micromouseonline/micromouse-timer/hardware/seven-segment-display/single-digit-mask-gray.png

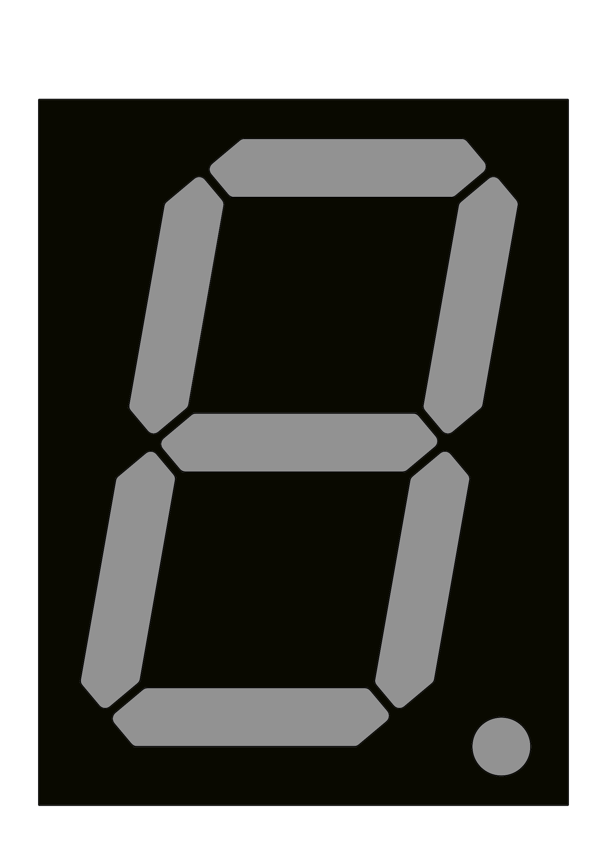
hardware/seven-segment-display/single-digit-mask-gray.png
