micromouseonline/micromouse-timer/images/controller-breadboard-prototype.jpg

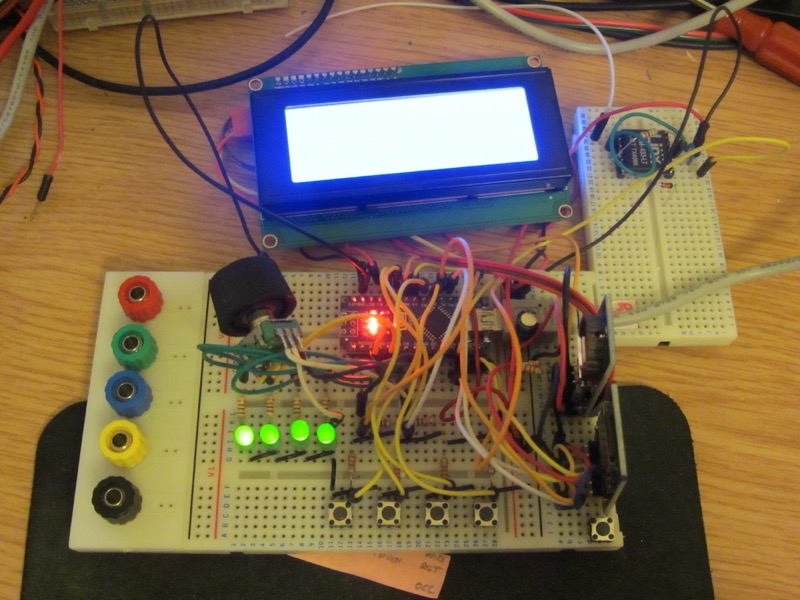
images/controller-breadboard-prototype.jpg
