micromouseonline/micromouse-timer/images/controller-panel-template.jpg

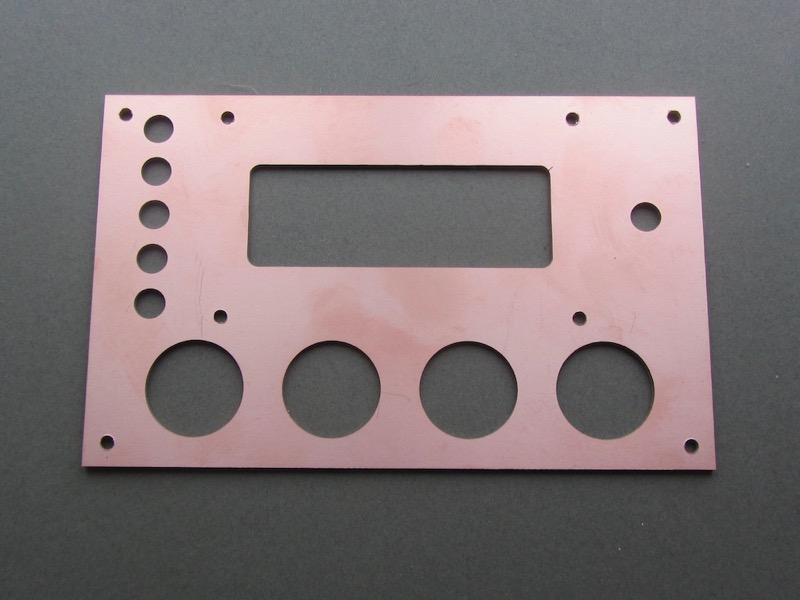
images/controller-panel-template.jpg
