micromouseonline/micromouse-timer/images/controller-render-V2.png

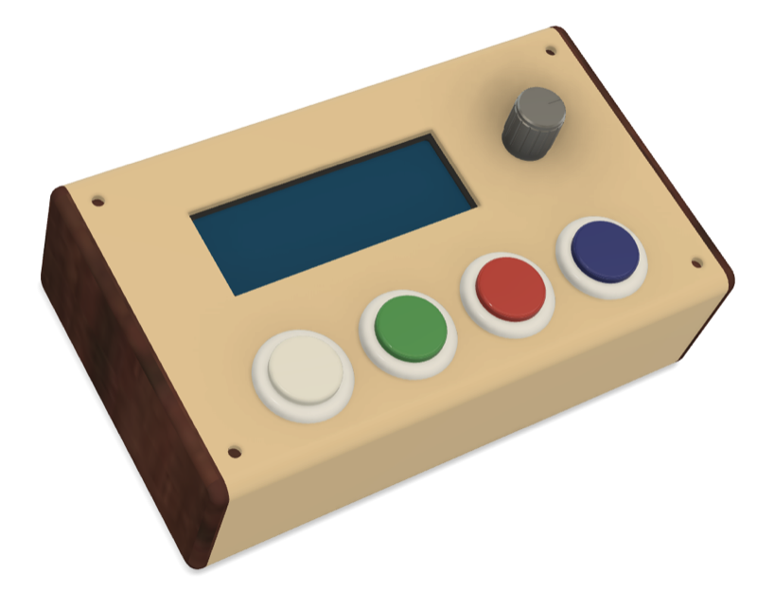
images/controller-render-V2.png
