micromouseonline/micromouse-timer/images/wall-pcb-with-led-holder.png

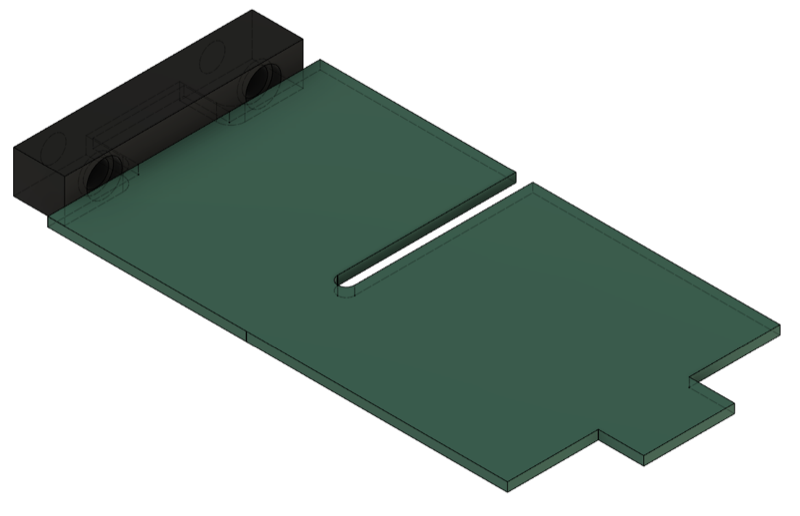
images/wall-pcb-with-led-holder.png
