micromouseonline/micromouse-timer/images/controller-assembly-prototype-parts.jpg

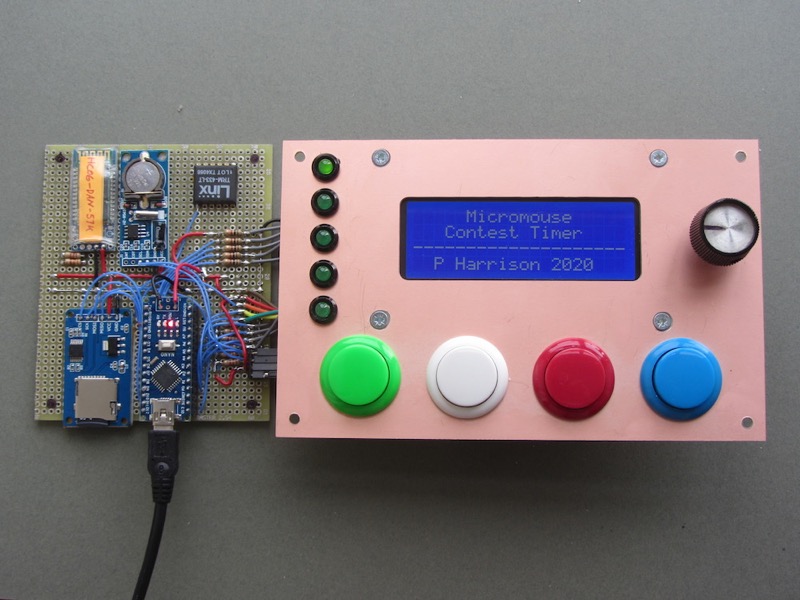
images/controller-assembly-prototype-parts.jpg
