micromouseonline/micromouse-timer/images/timing-gate-parts.jpg

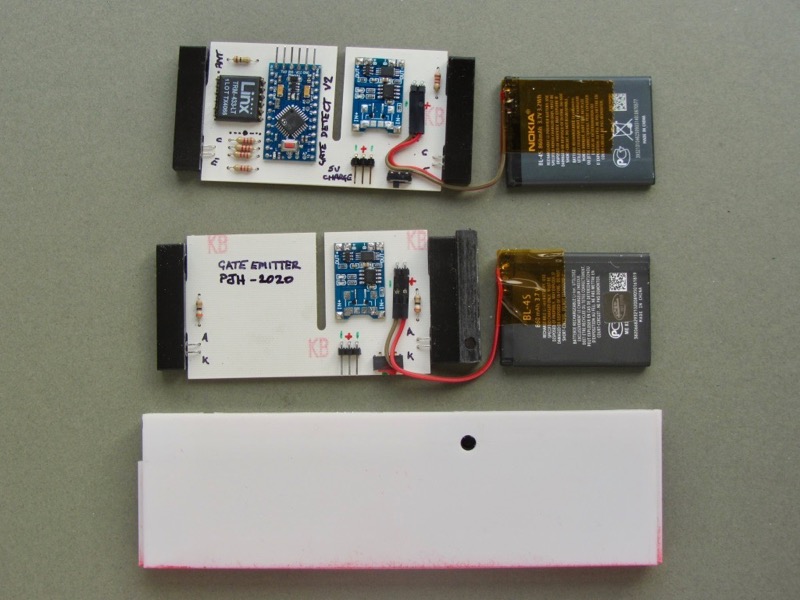
images/timing-gate-parts.jpg
