micromouseonline/micromouse-timer/hardware/gate-detector/gate-detector-mirrored (copy).dxf

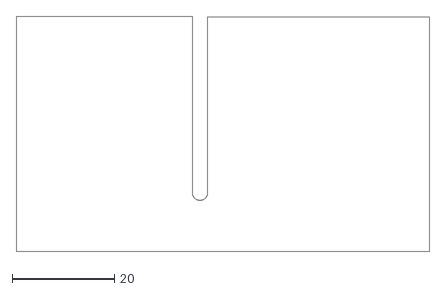
[picture p28: CAD file, 2023-07-05]
hardware/gate-detector/gate-detector-mirrored (copy).dxf
81.1 x 46.1
