micromouseonline/micromouse-timer/hardware/seven-segment-display/seven-segment-body-upright-milled.dxf

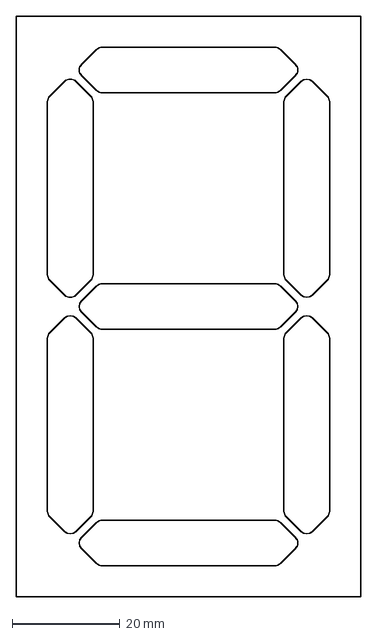
[picture p29: CAD file, 2023-07-05]
hardware/seven-segment-display/seven-segment-body-upright-milled.dxf
64.0 x 108.0 mm
