micromouseonline/micromouse-timer/hardware/controller-enclosure/controller-panel.stl

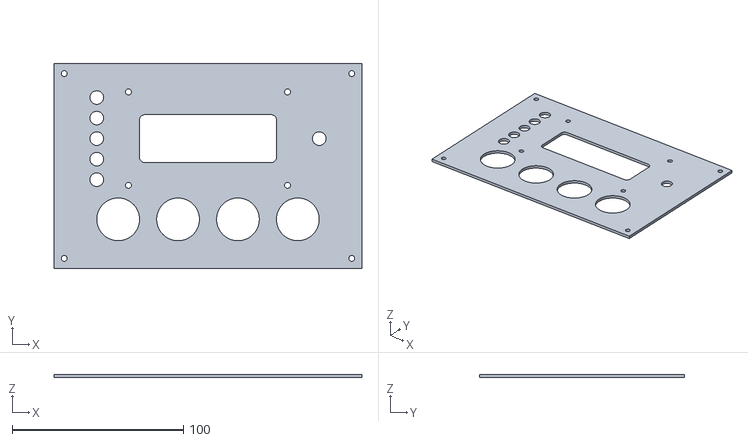
[picture p30: CAD file, 2023-07-05]
hardware/controller-enclosure/controller-panel.stl
180.0 x 120.0 x 2.00
