micromouseonline/micromouse-timer/hardware/controller-pcb/gate-controller-case-body.stl

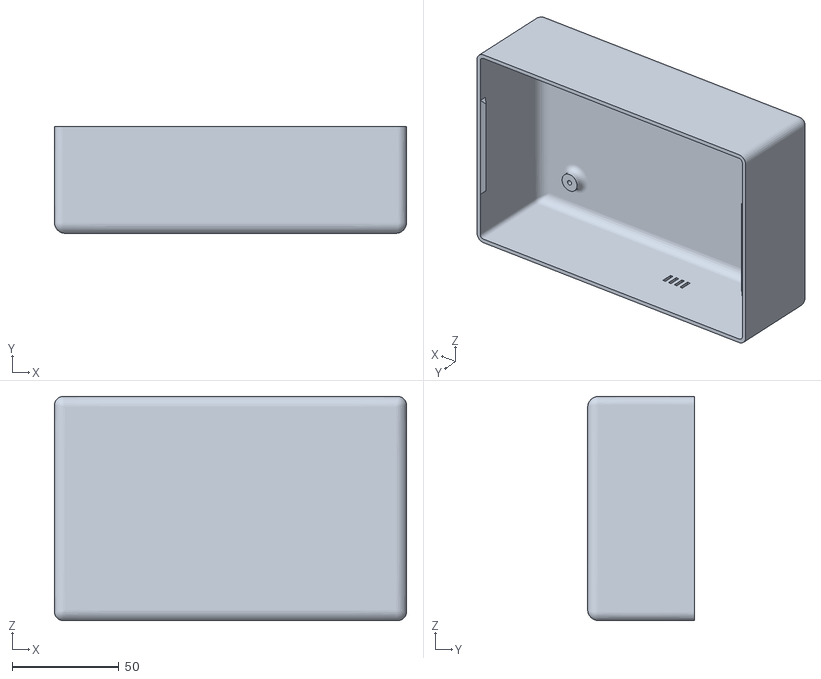
[picture p31: CAD file, 2023-07-05]
hardware/controller-pcb/gate-controller-case-body.stl
165.0 x 50.0 x 105.0
