micromouseonline/micromouse-timer/hardware/gate-charger/4-way-charger-brd-nofill.dxf

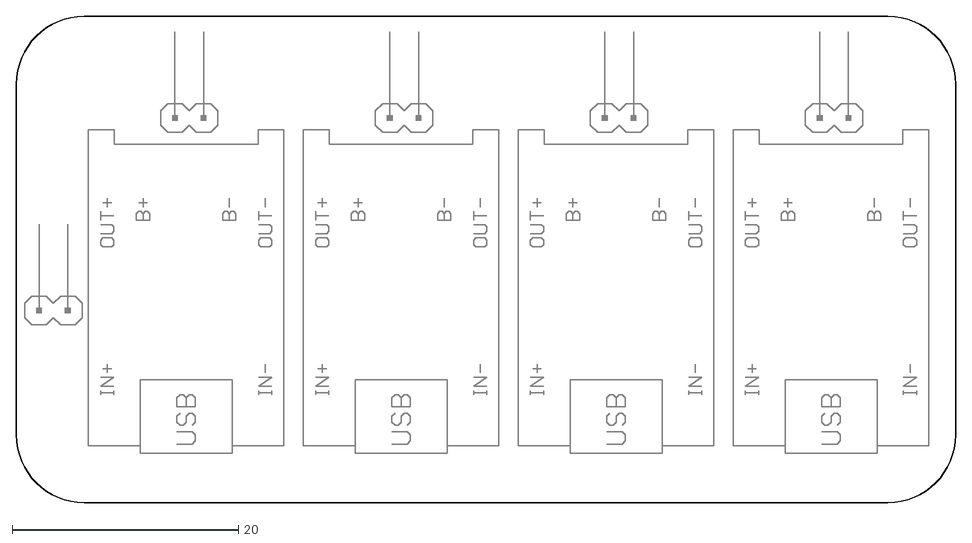
[picture p32: CAD file, 2023-07-05]
hardware/gate-charger/4-way-charger-brd-nofill.dxf
83.0 x 43.0
