micromouseonline/micromouse-timer/hardware/gate-detector/gate-detector-mirrored.dxf

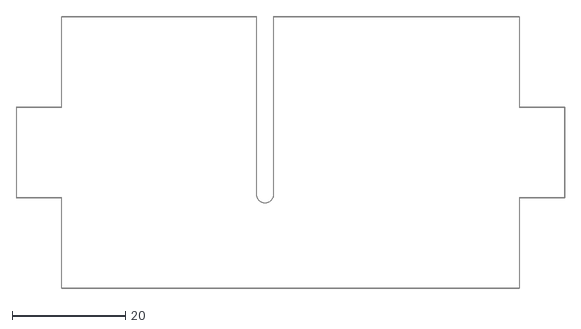
[picture p33: CAD file, 2023-07-05]
hardware/gate-detector/gate-detector-mirrored.dxf
97.1 x 48.1
