micromouseonline/micromouse-timer/hardware/gate-post-and-wall-parts/detector-holder.stl

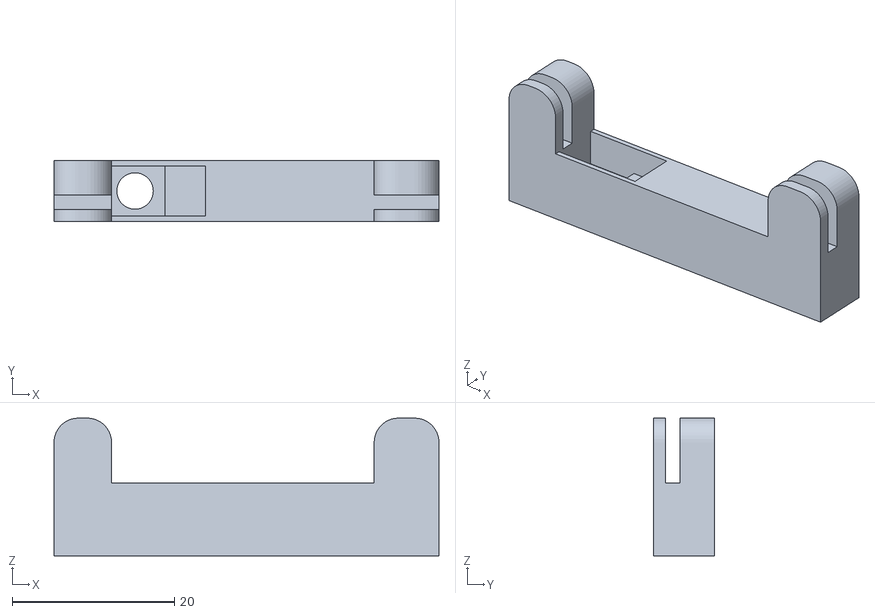
[picture p34: CAD file, 2023-07-05]
hardware/gate-post-and-wall-parts/detector-holder.stl
47.5 x 7.50 x 17.0
