micromouseonline/micromouse-timer/hardware/seven-segment-display/seven-segment-body-upright-segment.stl

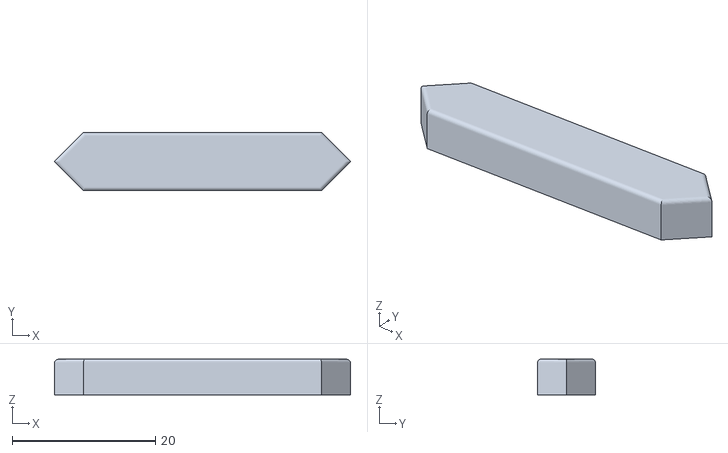
[picture p35: CAD file, 2023-07-05]
hardware/seven-segment-display/seven-segment-body-upright-segment.stl
41.3 x 8.10 x 5.00
