micromouseonline/micromouse-timer/hardware/controller-pcb/gate-controller-mirrored-V2.dxf

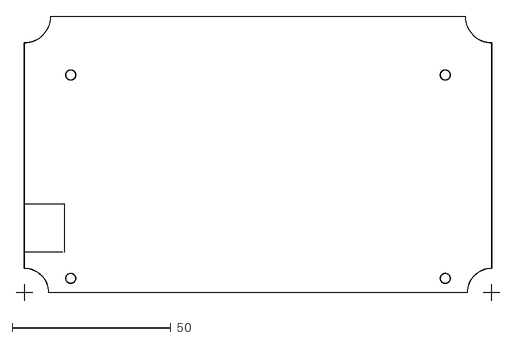
[picture p36: CAD file, 2023-07-05]
hardware/controller-pcb/gate-controller-mirrored-V2.dxf
152.6 x 89.8
