micromouseonline/micromouse-timer/hardware/gate-post-and-wall-parts/maze-gate-emitter-detector-holder-v2.stl

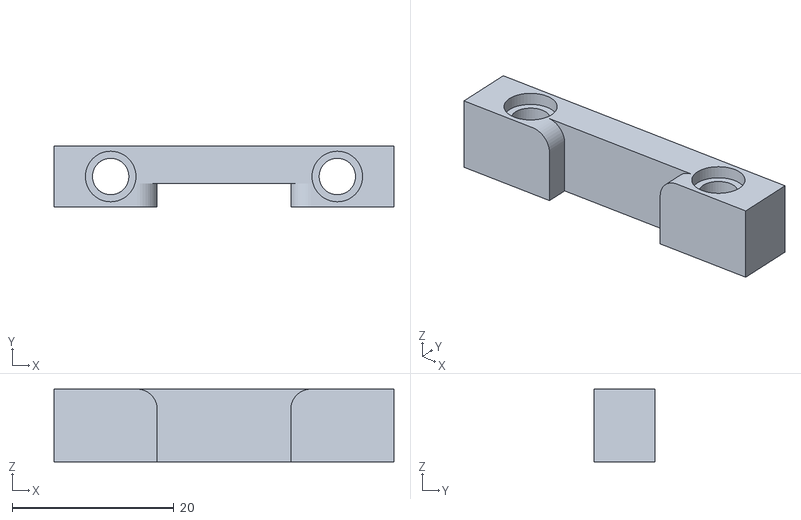
[picture p37: CAD file, 2023-07-05]
hardware/gate-post-and-wall-parts/maze-gate-emitter-detector-holder-v2.stl
42.0 x 7.50 x 9.00
