micromouseonline/micromouse-timer/hardware/seven-segment-display/vertical-segment.stl

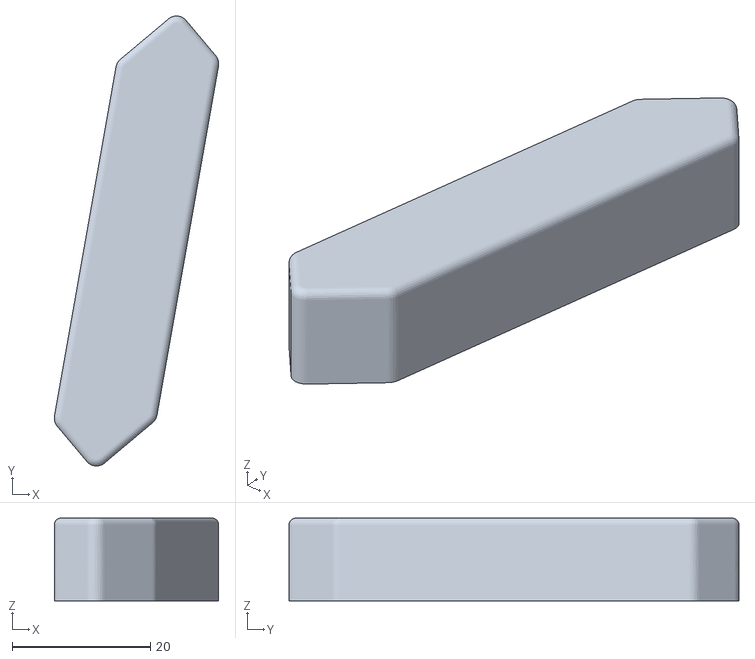
[picture p38: CAD file, 2023-07-05]
hardware/seven-segment-display/vertical-segment.stl
23.8 x 65.1 x 12.0
