micromouseonline/micromouse-timer/hardware/gate-post-and-wall-parts/post-half-double-sensor.stl

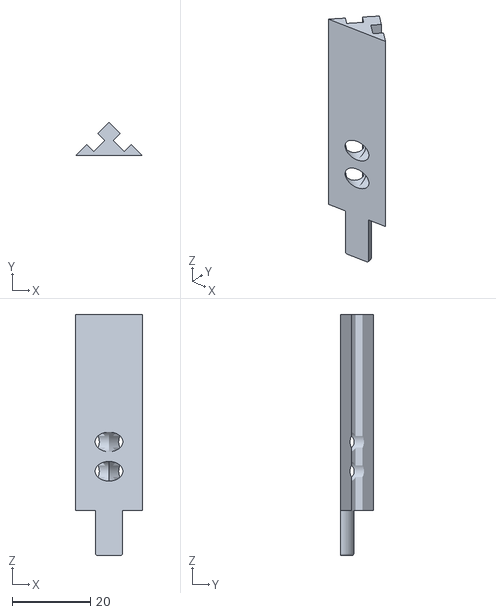
[picture p39: CAD file, 2023-07-05]
hardware/gate-post-and-wall-parts/post-half-double-sensor.stl
17.0 x 8.49 x 61.5
