micromouseonline/micromouse-timer/hardware/seven-segment-display/vertical-segment-small.stl

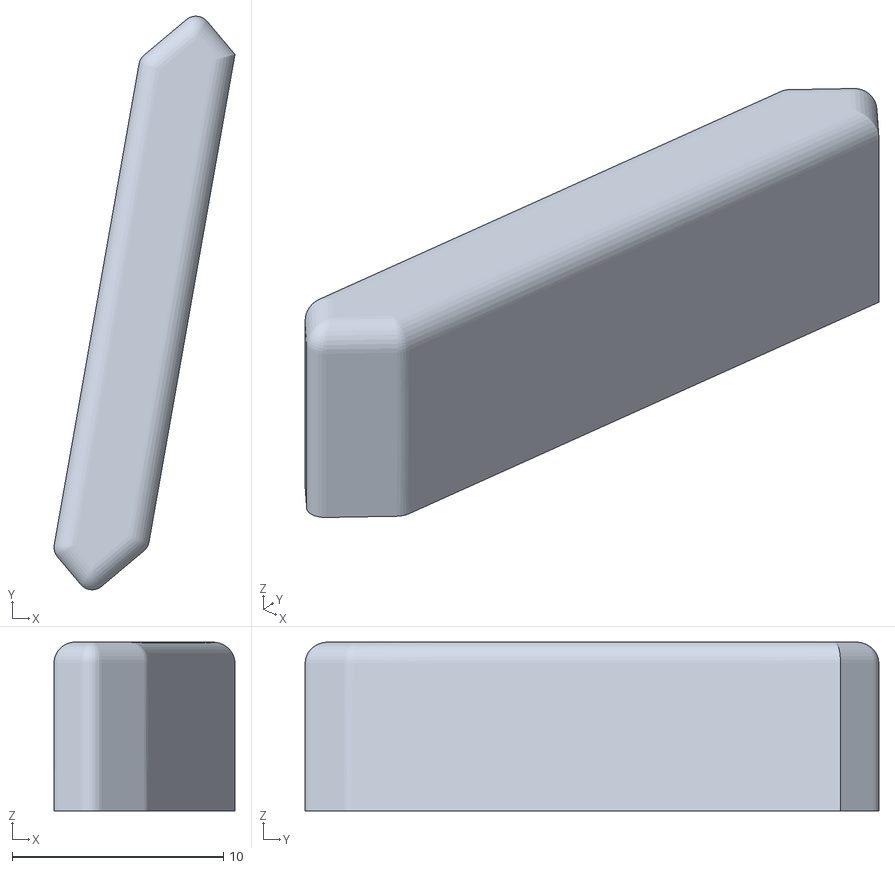
[picture p40: CAD file, 2023-07-05]
hardware/seven-segment-display/vertical-segment-small.stl
8.57 x 27.2 x 8.00
