micromouseonline/micromouse-timer/hardware/controller-enclosure/spacer-9.6mm.stl

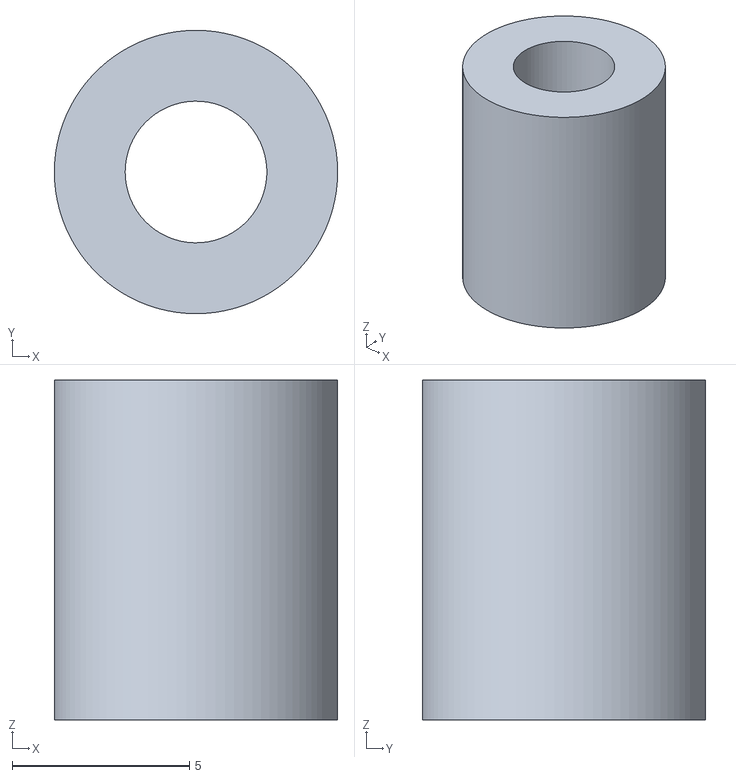
[picture p41: CAD file, 2023-07-05]
hardware/controller-enclosure/spacer-9.6mm.stl
8.00 x 8.00 x 9.60
