micromouseonline/micromouse-timer/hardware/gate-post-and-wall-parts/emitter-detector-twin-holder.stl

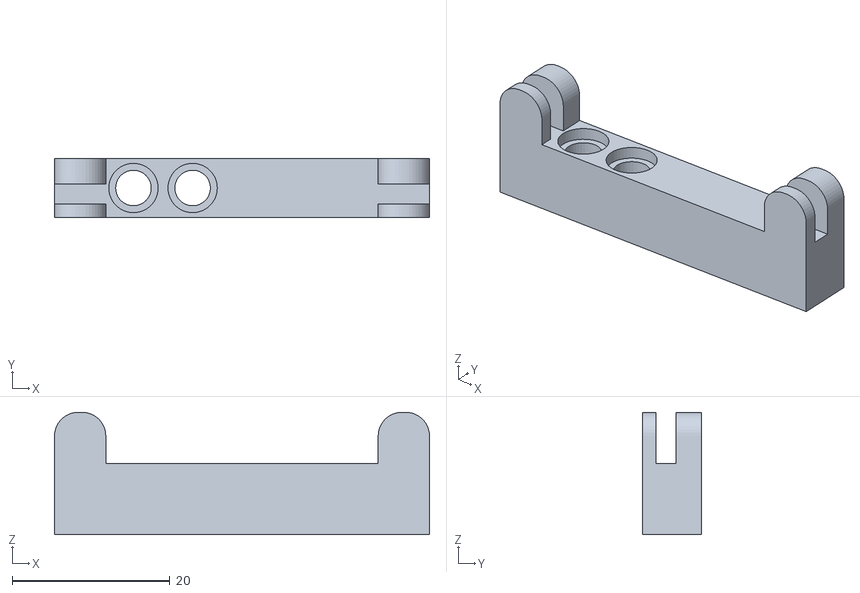
[picture p42: CAD file, 2023-07-05]
hardware/gate-post-and-wall-parts/emitter-detector-twin-holder.stl
47.5 x 7.50 x 15.5
