micromouseonline/micromouse-timer/hardware/seven-segment-display/seven-segment-body-small.stl

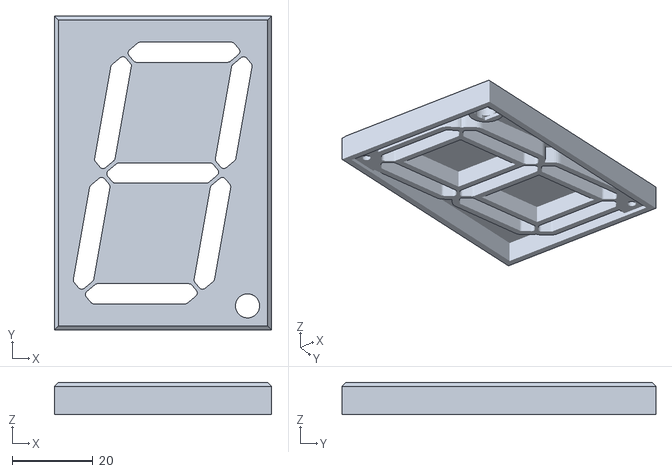
[picture p43: CAD file, 2023-07-05]
hardware/seven-segment-display/seven-segment-body-small.stl
54.0 x 78.0 x 8.00
