micromouseonline/micromouse-timer/hardware/gate-post-and-wall-parts/presence-reflector.stl

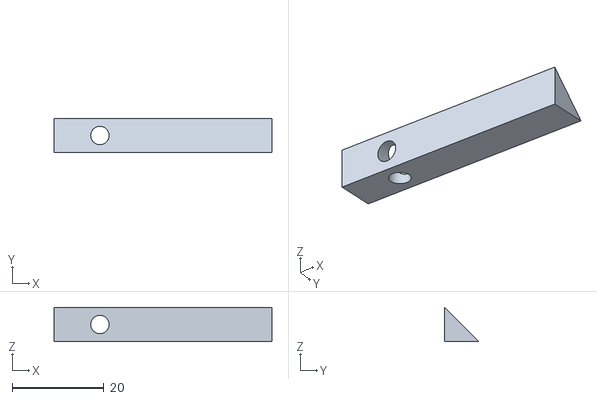
[picture p44: CAD file, 2023-07-05]
hardware/gate-post-and-wall-parts/presence-reflector.stl
47.5 x 7.50 x 7.50
