micromouseonline/micromouse-timer/hardware/seven-segment-display/single digit.dxf

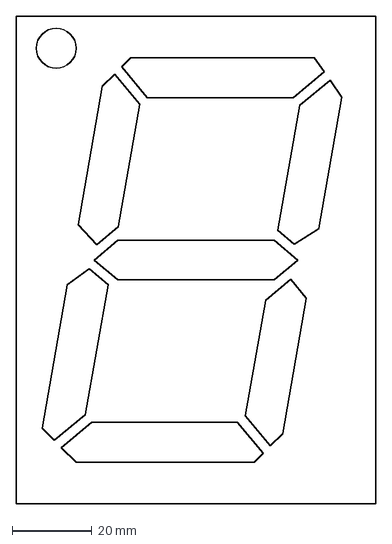
[picture p45: CAD file, 2023-07-05]
hardware/seven-segment-display/single digit.dxf
90.0 x 122.0 mm
