micromouseonline/micromouse-timer/hardware/controller-enclosure/gate-controller-V2.dxf

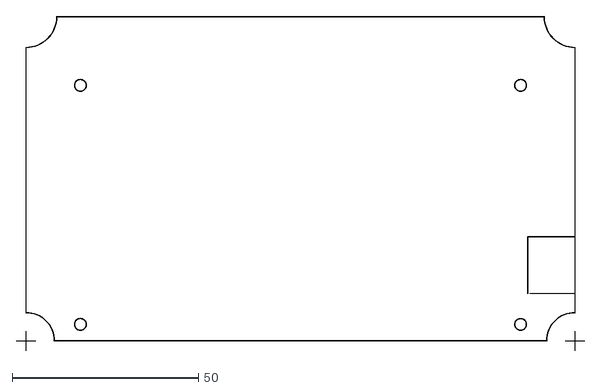
[picture p46: CAD file, 2023-07-05]
hardware/controller-enclosure/gate-controller-V2.dxf
152.6 x 89.8
