micromouseonline/micromouse-timer/hardware/gate-post-and-wall-parts/detector-holder-v2.stl

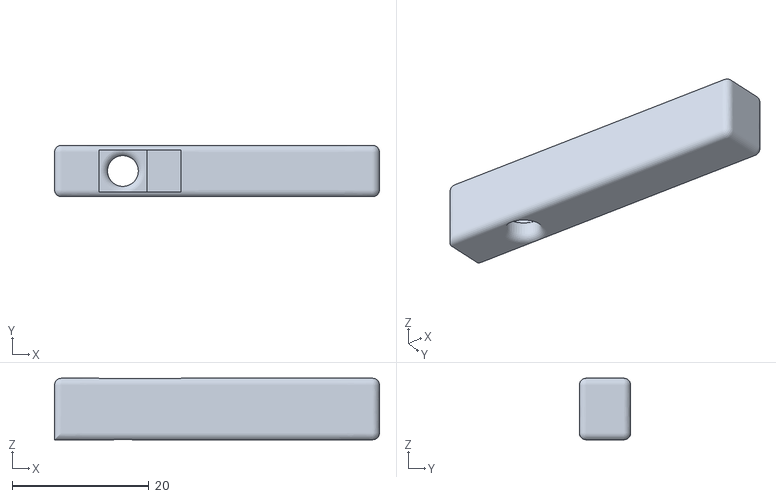
[picture p47: CAD file, 2023-07-05]
hardware/gate-post-and-wall-parts/detector-holder-v2.stl
47.5 x 7.50 x 9.00
