micromouseonline/micromouse-timer/hardware/seven-segment-display/display-connectors.dxf

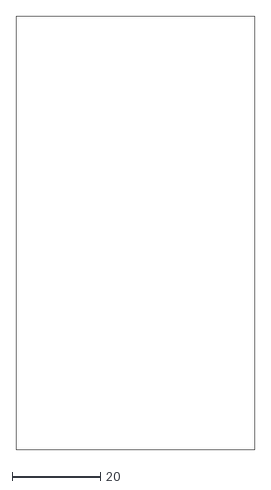
[picture p48: CAD file, 2023-07-05]
hardware/seven-segment-display/display-connectors.dxf
54.0 x 98.0
