micromouseonline/micromouse-timer/hardware/seven-segment-display/seven-segment-body-upright.stl

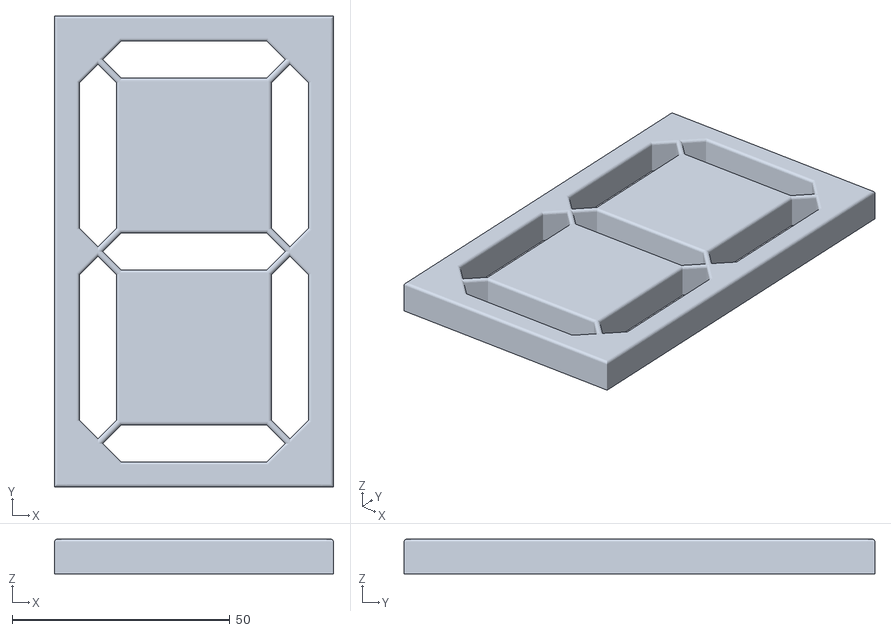
[picture p49: CAD file, 2023-07-05]
hardware/seven-segment-display/seven-segment-body-upright.stl
64.0 x 108.0 x 8.00
