micromouseonline/micromouse-timer/hardware/seven-segment-display/single-digit-seven-segment.dxf

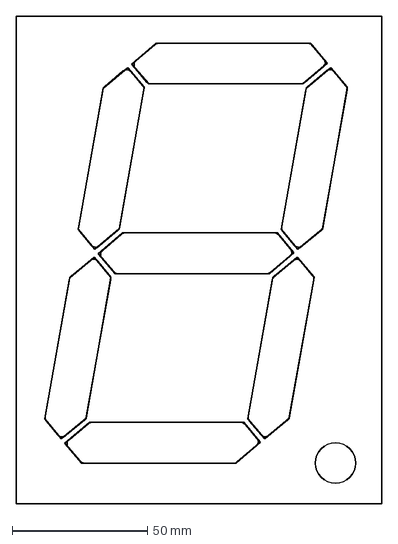
[picture p50: CAD file, 2023-07-05]
hardware/seven-segment-display/single-digit-seven-segment.dxf
135.0 x 180.0 mm
