micromouseonline/micromouse-timer/hardware/seven-segment-display/horizontal-segment.stl

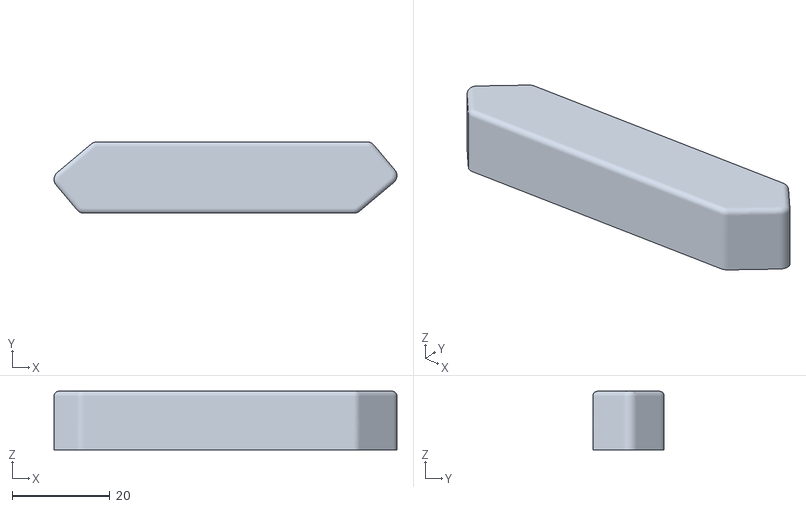
[picture p51: CAD file, 2023-07-05]
hardware/seven-segment-display/horizontal-segment.stl
70.1 x 14.6 x 12.0
