micromouseonline/micromouse-timer/hardware/seven-segment-display/horizontal-segment-small.stl

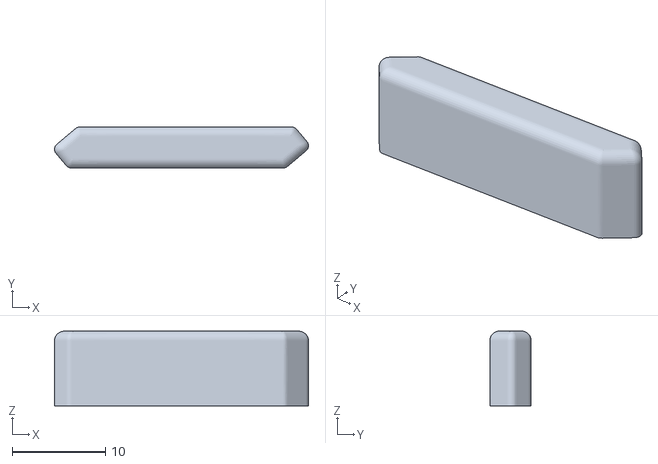
[picture p52: CAD file, 2023-07-05]
hardware/seven-segment-display/horizontal-segment-small.stl
27.2 x 4.40 x 8.00
