micromouseonline/micromouse-timer/hardware/seven-segment-display/display-board-outlines.dxf

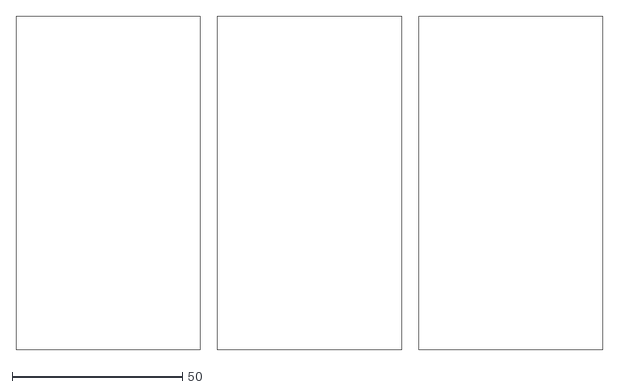
[picture p53: CAD file, 2023-07-05]
hardware/seven-segment-display/display-board-outlines.dxf
172.0 x 98.0
