micromouseonline/micromouse-timer/images/controller-assembly-prototype-box-rear.jpg

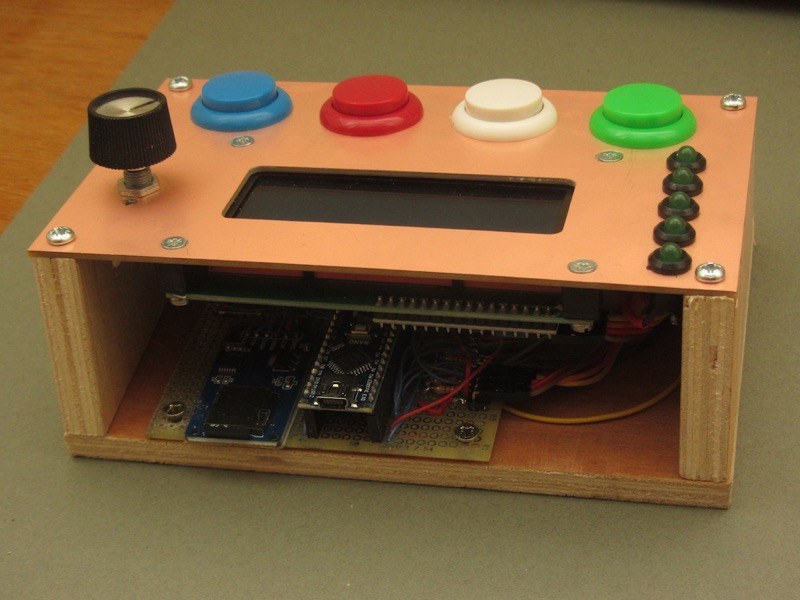
images/controller-assembly-prototype-box-rear.jpg
