micromouseonline/micromouse-timer/images/controller-assembly-prototype-box.jpg

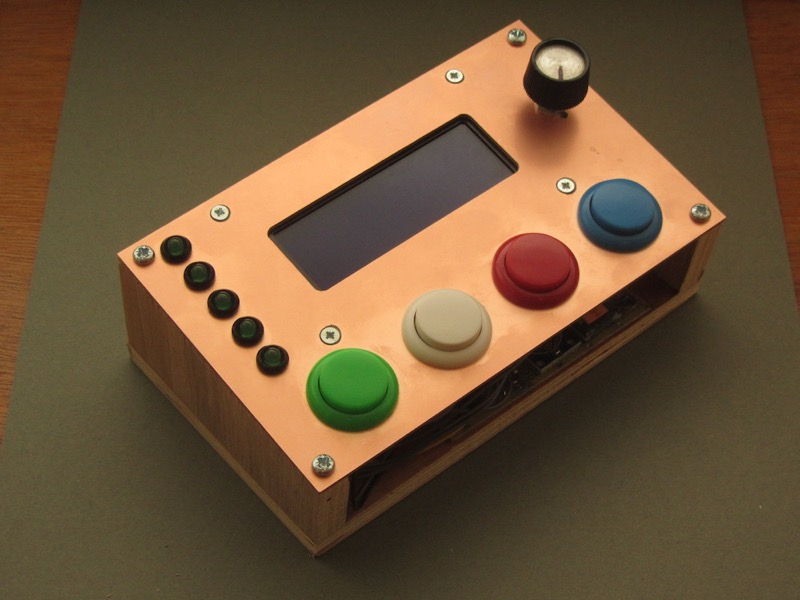
images/controller-assembly-prototype-box.jpg
