micromouseonline/micromouse-timer/images/controller-wiring.jpg

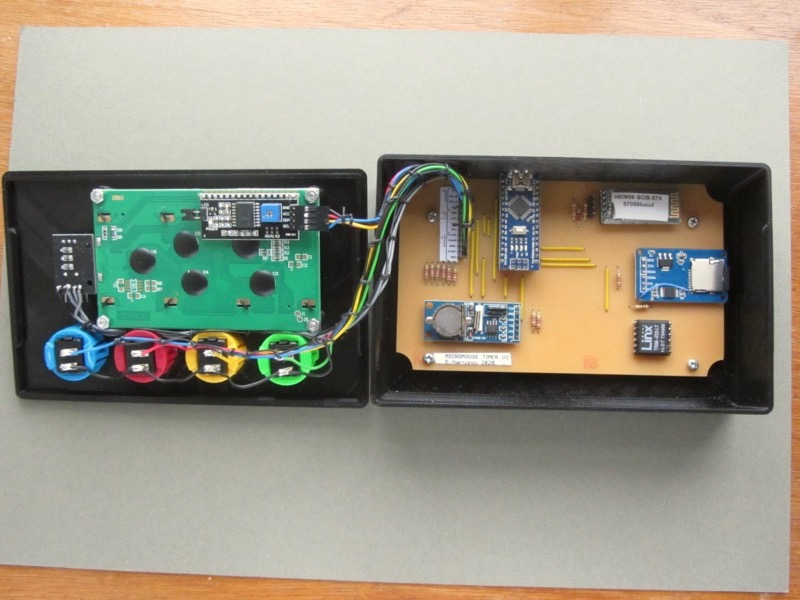
images/controller-wiring.jpg
